DesignGraveyard/V012_DIY_0-30V_0-1A_Lab_Power_Supply/LTSpice_Simulation/LM317_lab power supply.asc

C1: cap; 1µF; Rser=0.2
C2: cap; 100nF
C3: cap; 10nF
C4: cap; 10µ; Rser=1
C5: cap; 100µF; Rser=1
C6: cap; 10µF; Rser=0.3
C7: cap; 10µF
C8: cap; 1µF
C9: cap; 1µ
D1: diode; 1N4007
D2: diode; 1N4007
D3: diode; 1N4148
D4: diode; 1N4148
D5: diode; 1N4007
D6: diode; 1N4007
D7: diode; 1N4007
D8: LED; QTLP690C
P1: pot; Rtot=5k wiper=0.5
P2: pot; Rtot=1k wiper=.5
Q1: npn; 2N3904
R1: res; 1k
R2: res; 0.5
R3: res; 200
R4: res; 1
R5: res; 10k
R6: res; 1k
R7: res; 10k
R8: res; 2k2
R9: res; 270
R10: res; 240
R11: res; 10k
R12: res; 10k
R13: res; 470
U1: LM317-mod
U2: NE555
U3: LM317-mod
U4: LM317-mod
V1: voltage; PULSE(0 18 0 10u); Rser=0.1
V2: voltage; PULSE(50 0.1 100m 10m 50m 1); Rser=0.1
Named nets: 0, MID, Vminus, Vin, 12Vaux, Vout
.tran 250m startup
The bias current of the LM317 is 1.25V/240 ohm = ~5mA
So the negative current must be ~10mA -1k/10V is ok
C9 reduces the output ripple to 50uV pp
